L4m4L/LED_Glasses/firmware/rave_shades/src/main.c

#include "audio.h"
#include "button.h"
#include "display.h"
#include "system.h"
#include "util.h"

static context_t global_context = {0};

static void button_pressed_callback(context_t *context);

int main(void)
{
    global_context.display_mode = DISPLAY_MODE_WATERFALL;

    system_init_pll_hsi16_53();

    audio_init();
    button_init(button_pressed_callback);
    display_init();

    while (1)
    {
        audio_run(&global_context);
        display_run(&global_context);
        button_run(&global_context);
    }
}

void button_pressed_callback(context_t *context)
{
    switch (context->display_mode)
    {
    case DISPLAY_MODE_DEFAULT:
        context->display_mode = DISPLAY_MODE_HEART;
        break;
    case DISPLAY_MODE_HEART:
        context->display_mode = DISPLAY_MODE_WATERFALL;
        break;
    case DISPLAY_MODE_WATERFALL:
        context->display_mode = DISPLAY_MODE_LACHLAN;
        break;
    case DISPLAY_MODE_LACHLAN:
        context->display_mode = DISPLAY_MODE_DEFAULT;
        break;
    default:
        context->display_mode = DISPLAY_MODE_DEFAULT;
    }
}
